steve-chamberlin/backwoods-logger/blsync/board.png

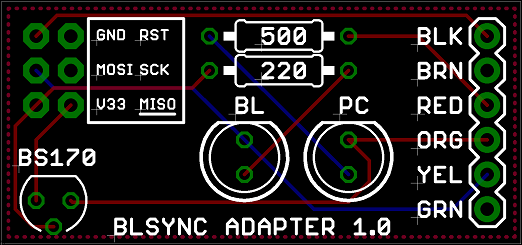
blsync/board.png
