steve-chamberlin/backwoods-logger/Logger Classic files/board-bottom.png

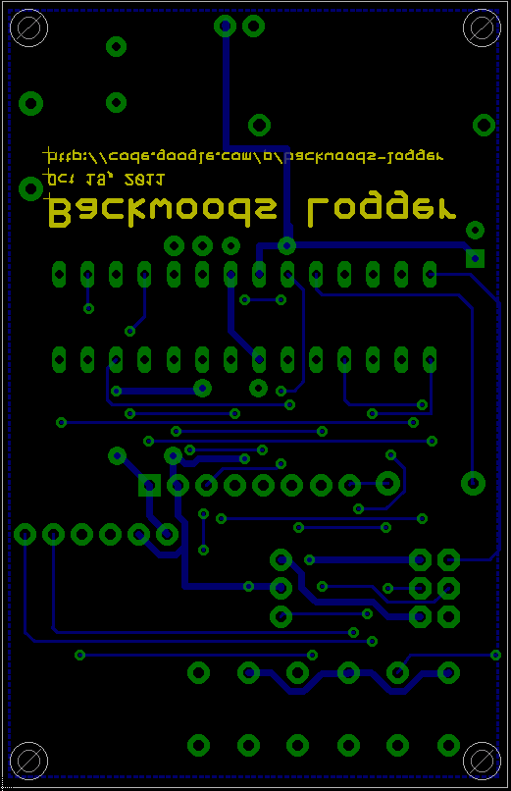
Logger Classic files/board-bottom.png
