steve-chamberlin/backwoods-logger/i2c.c

/*
 * ----------------------------------------------------------------------------
 * "THE BEER-WARE LICENSE" (Revision 42):
 * <joerg@FreeBSD.ORG> wrote this file.  As long as you retain this notice you
 * can do whatever you want with this stuff. If we meet some day, and you think
 * this stuff is worth it, you can buy me a beer in return.        Joerg Wunsch
 * ----------------------------------------------------------------------------
 */
/* Modified for use with BMP085 sensor by Steve Chamberlin */

#include <inttypes.h>
#include <stdio.h>
#include <stdlib.h>

#include <avr/io.h>
#include <util/twi.h>		/* Note [1] */

/*
 * Maximal number of iterations to wait for a device to respond for a
 * selection.  Should be large enough to allow for a pending write to
 * complete, but low enough to properly abort an infinite loop in case
 * a slave is broken or not present at all.  With 100 kHz TWI clock,
 * transfering the start condition and SLA+R/W packet takes about 10
 * µs.  The longest write period is supposed to not exceed ~ 10 ms.
 * Thus, normal operation should not require more than 100 iterations
 * to get the device to respond to a selection.
 */
#define MAX_ITER 200

/*
 * Saved TWI status register, for error messages only.  We need to
 * save it in a variable, since the datasheet only guarantees the TWSR
 * register to have valid contents while the TWINT bit in TWCR is set.
 */
uint8_t twst;

/* TWI address of the slave to communicate with */
uint8_t slaveAddr;

void i2cSetAddress(uint8_t _slaveAddr)
{
	slaveAddr = _slaveAddr;
}

/*
 * Do all the startup-time peripheral initializations: TWI clock.
 */
void
i2cInit(void)
{
  /* initialize TWI clock: 100 kHz clock, TWPS = 0 => prescaler = 1 */
#if defined(TWPS0)
  /* has prescaler (mega128 & newer) */
  TWSR = 0;
#endif

#if F_CPU < 3600000UL
  TWBR = 10;			/* smallest TWBR value, see note [5] */
#else
  TWBR = (F_CPU / 100000UL - 16) / 2;
#endif
}

/*
 * Note [7]
 *
 * Read "len" bytes from register at "addr" into "buf".
 *
 * This requires two bus cycles: during the first cycle, the device
 * will be selected (master transmitter mode), and the address
 * transfered.
 *
 * The second bus cycle will reselect the device (repeated start
 * condition, going into master receiver mode), and transfer the data
 * from the device to the TWI master.  Multiple bytes can be
 * transfered by ACKing the client's transfer.  The last transfer will
 * be NACKed, which the client will take as an indication to not
 * initiate further transfers.
 *
 * Returns the number of bytes read if successful, else returns 0.
 */
uint8_t
i2cReadBytes(uint16_t addr, int len, uint8_t *buf)
{
  uint8_t sla, twcr;
  uint8_t rv = 0;
  uint8_t n = 0;
  
  sla = slaveAddr;

  /*
   * Note [8]
   * First cycle: master transmitter mode
   */
  restart:
  if (n++ >= MAX_ITER)
    return 0;
  begin:

  TWCR = _BV(TWINT) | _BV(TWSTA) | _BV(TWEN); /* send start condition */
  while ((TWCR & _BV(TWINT)) == 0) ; /* wait for transmission */
  switch ((twst = TW_STATUS))
    {
    case TW_REP_START:		/* OK, but should not happen */
    case TW_START:
      break;

    case TW_MT_ARB_LOST:	/* Note [9] */
      goto begin;

    default:
      return 0;		/* error: not in start condition */
				/* NB: do /not/ send stop condition */
    }

  /* Note [10] */
  /* send SLA+W */
  TWDR = sla | TW_WRITE;
  TWCR = _BV(TWINT) | _BV(TWEN); /* clear interrupt to start transmission */
  while ((TWCR & _BV(TWINT)) == 0) ; /* wait for transmission */
  switch ((twst = TW_STATUS))
    {
    case TW_MT_SLA_ACK:
      break;

    case TW_MT_SLA_NACK:	/* nack during select: device busy writing */
				/* Note [11] */
      goto restart;

    case TW_MT_ARB_LOST:	/* re-arbitrate */
      goto begin;

    default:
      goto error;		/* must send stop condition */
    }

  TWDR = addr;		/* low 8 bits of addr */
  TWCR = _BV(TWINT) | _BV(TWEN); /* clear interrupt to start transmission */
  while ((TWCR & _BV(TWINT)) == 0) ; /* wait for transmission */
  switch ((twst = TW_STATUS))
    {
    case TW_MT_DATA_ACK:
      break;

    case TW_MT_DATA_NACK:
      goto quit;

    case TW_MT_ARB_LOST:
      goto begin;

    default:
      goto error;		/* must send stop condition */
    }

  /*
   * Note [12]
   * Next cycle(s): master receiver mode
   */
  TWCR = _BV(TWINT) | _BV(TWSTA) | _BV(TWEN); /* send (rep.) start condition */
  while ((TWCR & _BV(TWINT)) == 0) ; /* wait for transmission */
  switch ((twst = TW_STATUS))
    {
    case TW_START:		/* OK, but should not happen */
    case TW_REP_START:
      break;

    case TW_MT_ARB_LOST:
      goto begin;

    default:
      goto error;
    }

  /* send SLA+R */
  TWDR = sla | TW_READ;
  TWCR = _BV(TWINT) | _BV(TWEN); /* clear interrupt to start transmission */
  while ((TWCR & _BV(TWINT)) == 0) ; /* wait for transmission */
  switch ((twst = TW_STATUS))
    {
    case TW_MR_SLA_ACK:
      break;

    case TW_MR_SLA_NACK:
      goto quit;

    case TW_MR_ARB_LOST:
      goto begin;

    default:
      goto error;
    }

  for (twcr = _BV(TWINT) | _BV(TWEN) | _BV(TWEA) /* Note [13] */;
       len > 0;
       len--)
    {
      if (len == 1)
	twcr = _BV(TWINT) | _BV(TWEN); /* send NAK this time */
      TWCR = twcr;		/* clear int to start transmission */
      while ((TWCR & _BV(TWINT)) == 0) ; /* wait for transmission */
      switch ((twst = TW_STATUS))
	{
	case TW_MR_DATA_NACK:
	  len = 0;		/* force end of loop */
	  /* FALLTHROUGH */
	case TW_MR_DATA_ACK:
	  *buf++ = TWDR;
	  rv++;
	  break;

	default:
	  goto error;
	}
    }
  quit:
  /* Note [14] */
  TWCR = _BV(TWINT) | _BV(TWSTO) | _BV(TWEN); /* send stop condition */

  return rv;

  error:
  rv = 0;
  goto quit;
}

/*
 * Write 1 byte into register at "addr" from "val".
 *
 * This is a bit simpler than the previous function since both, the
 * address and the data bytes will be transfered in master transmitter
 * mode, thus no reselection of the device is necessary. 
 *
 * Returns the number of bytes written if successful, else returns 0.
 */
uint8_t
i2cWriteByte(uint16_t addr, uint8_t val)
{
  uint8_t sla;
  uint8_t rv = 0;
  uint8_t n = 0;
  
  sla = slaveAddr;

  restart:
  if (n++ >= MAX_ITER)
    return 0;
  begin:

  /* Note [15] */
  TWCR = _BV(TWINT) | _BV(TWSTA) | _BV(TWEN); /* send start condition */
  while ((TWCR & _BV(TWINT)) == 0) ; /* wait for transmission */
  switch ((twst = TW_STATUS))
    {
    case TW_REP_START:		/* OK, but should not happen */
    case TW_START:
      break;

    case TW_MT_ARB_LOST:
      goto begin;

    default:
      return 0;		/* error: not in start condition */
				/* NB: do /not/ send stop condition */
    }

  /* send SLA+W */
  TWDR = sla | TW_WRITE;
  TWCR = _BV(TWINT) | _BV(TWEN); /* clear interrupt to start transmission */
  while ((TWCR & _BV(TWINT)) == 0) ; /* wait for transmission */
  switch ((twst = TW_STATUS))
    {
    case TW_MT_SLA_ACK:
      break;

    case TW_MT_SLA_NACK:	/* nack during select: device busy writing */
      goto restart;

    case TW_MT_ARB_LOST:	/* re-arbitrate */
      goto begin;

    default:
      goto error;		/* must send stop condition */
    }

  TWDR = addr;		/* low 8 bits of addr */
  TWCR = _BV(TWINT) | _BV(TWEN); /* clear interrupt to start transmission */
  while ((TWCR & _BV(TWINT)) == 0) ; /* wait for transmission */
  switch ((twst = TW_STATUS))
    {
    case TW_MT_DATA_ACK:
      break;

    case TW_MT_DATA_NACK:
      goto quit;

    case TW_MT_ARB_LOST:
      goto begin;

    default:
      goto error;		/* must send stop condition */
    }


  TWDR = val;
  TWCR = _BV(TWINT) | _BV(TWEN); /* start transmission */
  while ((TWCR & _BV(TWINT)) == 0) ; /* wait for transmission */
  switch ((twst = TW_STATUS))
	{
	case TW_MT_DATA_NACK:
	  goto error;		/* device write protected -- Note [16] */

	case TW_MT_DATA_ACK:
	  rv = 1;
	  break;

	default:
	  goto error;
	}
    
  quit:
  TWCR = _BV(TWINT) | _BV(TWSTO) | _BV(TWEN); /* send stop condition */

  return rv;

  error:
  rv = 0;
  goto quit;
}
